vrbadev/Ultrasound_Test_Prototype/STM32CubeIDE/Ultrasound_Test_Prototype/Core/Src/main.c

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
/* Includes ------------------------------------------------------------------*/
#include "main.h"

/* USER CODE BEGIN Includes */
#include <stdio.h>
#include <stdbool.h>
#include <stdlib.h>
/* USER CODE END Includes */

/* USER CODE BEGIN PD */
#ifdef __GNUC__
#define PUTCHAR_PROTOTYPE int __io_putchar(int ch)
#else
#define PUTCHAR_PROTOTYPE int fputc(int ch, FILE *f)
#endif

#define ADC_BUFFER_LEN 1000
#define USART_RX_BUFFER_LEN 256

#define MAX9939_SHDN (0x01 << 7)
#define MAX9939_MEAS (0x01 << 6)

#define MAX9939_VOS_NEG (0x01 << 5)
#define MAX9939_VOS_0_0MV (0x00 << 1)
#define MAX9939_VOS_1_3MV (0x01 << 1)
#define MAX9939_VOS_2_5MV (0x02 << 1)
#define MAX9939_VOS_3_8MV (0x03 << 1)
#define MAX9939_VOS_4_9MV (0x04 << 1)
#define MAX9939_VOS_6_1MV (0x05 << 1)
#define MAX9939_VOS_7_3MV (0x06 << 1)
#define MAX9939_VOS_8_4MV (0x07 << 1)
#define MAX9939_VOS_10_6MV (0x08 << 1)
#define MAX9939_VOS_11_7MV (0x09 << 1)
#define MAX9939_VOS_12_7MV (0x0A << 1)
#define MAX9939_VOS_13_7MV (0x0B << 1)
#define MAX9939_VOS_14_7MV (0x0C << 1)
#define MAX9939_VOS_15_7MV (0x0D << 1)
#define MAX9939_VOS_16_7MV (0x0E << 1)
#define MAX9939_VOS_17_6MV (0x0F << 1)

#define MAX9939_GAIN_0_25X ((0x09 << 1) | 0x01)
#define MAX9939_GAIN_1X ((0x00 << 1) | 0x01)
#define MAX9939_GAIN_10X ((0x01 << 1) | 0x01)
#define MAX9939_GAIN_20X ((0x02 << 1) | 0x01)
#define MAX9939_GAIN_30X ((0x03 << 1) | 0x01)
#define MAX9939_GAIN_40X ((0x04 << 1) | 0x01)
#define MAX9939_GAIN_60X ((0x05 << 1) | 0x01)
#define MAX9939_GAIN_80X ((0x06 << 1) | 0x01)
#define MAX9939_GAIN_120X ((0x07 << 1) | 0x01)
#define MAX9939_GAIN_157X ((0x08 << 1) | 0x01)

/* USER CODE END PD */

ADC_HandleTypeDef hadc1;
DMA_HandleTypeDef hdma_adc1;

SPI_HandleTypeDef hspi1;

TIM_HandleTypeDef htim3;

UART_HandleTypeDef huart1;
DMA_HandleTypeDef hdma_usart1_rx;
DMA_HandleTypeDef hdma_usart1_tx;

/* USER CODE BEGIN PV */
uint32_t millis = 0;
uint32_t delay_end = 0;

uint8_t usart_rx_buffer[USART_RX_BUFFER_LEN];
uint32_t usart_rx_len = 0;

struct {
	uint8_t delimeter[5];
	uint8_t pga_gain : 8;
	int8_t pga_offset : 8;
	uint8_t adc_channel : 8;
	uint32_t id : 32;
	uint8_t adc_buffer[(3 * ADC_BUFFER_LEN) / 4];
	uint8_t dummy[2];
} usart_tx_packet;

uint32_t adc_num_conversions = 0;
uint16_t adc_buffer[ADC_BUFFER_LEN];
bool adc_dma_half_complete = false;
bool adc_dma_complete = false;

struct {
	uint8_t shdn;
	uint8_t meas;
	int gain;
	int offset;
} max9939_settings;

struct {
	char shdn_ch;
	char meas_ch;
	char* gain_str;
	char offset_sign;
	char* offset_str;
} max9939_info;
/* USER CODE END PV */

void SystemClock_Config(void);
static void MX_GPIO_Init(void);
static void MX_DMA_Init(void);
static void MX_ADC1_Init(void);
static void MX_SPI1_Init(void);
static void MX_USART1_UART_Init(void);
static void MX_TIM3_Init(void);
/* USER CODE BEGIN 0 */
PUTCHAR_PROTOTYPE {
	HAL_UART_Transmit(&huart1, (uint8_t*) &ch, 1, HAL_MAX_DELAY);
	return ch;
}

void delay(uint32_t ms) {
	delay_end = millis + ms;
	while (millis < delay_end);
}

void adc_set_channel(uint32_t ch)
{
	HAL_ADC_Stop_DMA(&hadc1);
	ADC_ChannelConfTypeDef sConfig = {0};
	sConfig.Channel = ch;
	sConfig.Rank = ADC_REGULAR_RANK_1;
	sConfig.SamplingTime = ADC_SAMPLINGTIME_COMMON_1;
	if (HAL_ADC_ConfigChannel(&hadc1, &sConfig) != HAL_OK)
	{
	Error_Handler();
	}
	HAL_ADC_Start_DMA(&hadc1, (uint32_t*) adc_buffer, ADC_BUFFER_LEN);
}

void compress_12bit_data(bool first_half)
{
	uint16_t* start = first_half ? (uint16_t*) adc_buffer : (uint16_t*) &(adc_buffer[ADC_BUFFER_LEN/2]);
	uint32_t o = 0;
	for (uint32_t i = 0; i < ADC_BUFFER_LEN / 2; i+=2) {
		usart_tx_packet.adc_buffer[o] = (uint8_t) (start[i] & 0x00FF);
		o++;
		usart_tx_packet.adc_buffer[o] = (uint8_t) ((start[i] & 0x0F00) >> 8) | ((start[i+1] & 0x0F00) >> 4);
		o++;
		usart_tx_packet.adc_buffer[o] = (uint8_t) (start[i+1] & 0x00FF);
		o++;
	}
	usart_tx_packet.id++;
}

void max9939_write(uint8_t reg)
{
	HAL_GPIO_WritePin(SPI1_NSS_GPIO_Port, SPI1_NSS_Pin, GPIO_PIN_RESET);
	delay(1);
	HAL_SPI_Transmit(&hspi1, &reg, 1, HAL_MAX_DELAY);
	while (hspi1.State == HAL_SPI_STATE_BUSY);
	HAL_GPIO_WritePin(SPI1_NSS_GPIO_Port, SPI1_NSS_Pin, GPIO_PIN_SET);
	delay(1);
}

void max9939_apply_settings()
{
	max9939_write((((uint8_t) max9939_settings.gain) << 1) | 0x01);

	int tmp = max9939_settings.offset;
	if (tmp < 0) {
		tmp = -tmp;
		if (tmp >= 0 && tmp <= 15) {
			max9939_write(max9939_settings.shdn | max9939_settings.meas | ((((uint8_t) tmp) << 1) | MAX9939_VOS_NEG));
		}
	} else {
		if (tmp >= 0 && tmp <= 15) {
			max9939_write(max9939_settings.shdn | max9939_settings.meas | (((uint8_t) tmp) << 1));
		}
	}
}

/* USER CODE END 0 */

/**
  * @brief  The application entry point.
  * @retval int
  */
int main(void)
{
  /* MCU Configuration--------------------------------------------------------*/

  /* Reset of all peripherals, Initializes the Flash interface and the Systick. */
  HAL_Init();

  /* Configure the system clock */
  SystemClock_Config();

  /* Initialize all configured peripherals */
  MX_GPIO_Init();
  MX_DMA_Init();
  MX_ADC1_Init();
  MX_SPI1_Init();
  MX_USART1_UART_Init();
  MX_TIM3_Init();
  /* USER CODE BEGIN 2 */
  //HAL_ADC_Start_IT(&hadc1);
  HAL_TIM_PWM_Start(&htim3, TIM_CHANNEL_1);

  HAL_UART_Receive_DMA(&huart1, usart_rx_buffer, USART_RX_BUFFER_LEN);

  max9939_settings.shdn = 0x00;
  max9939_settings.meas = 0x00;
  max9939_settings.gain = 8;
  max9939_settings.offset = 10;
  max9939_apply_settings();

  for(int i = 0; i < sizeof(usart_tx_packet.delimeter); i++) { usart_tx_packet.delimeter[i] = 0xFF; }
  usart_tx_packet.id = 0;
  usart_tx_packet.adc_channel = 2;
  usart_tx_packet.pga_gain = (uint8_t) max9939_settings.gain;
  usart_tx_packet.pga_offset = (int8_t) max9939_settings.offset;

  HAL_ADC_Start_DMA(&hadc1, (uint32_t*) adc_buffer, ADC_BUFFER_LEN);

  HAL_GPIO_WritePin(LED_GPIO_Port, LED_Pin, GPIO_PIN_SET);
  /* USER CODE END 2 */

  /* Infinite loop */
  /* USER CODE BEGIN WHILE */
  int tmp;

  while (1)
  {
    /* USER CODE END WHILE */

    /* USER CODE BEGIN 3 */
	if (usart_rx_len > 0) {
		//printf("Received message: %lu\n", usart_rx_len);
		//HAL_UART_Transmit_DMA(&huart1, usart_rx_buffer, usart_rx_len); // echo
		switch (usart_rx_buffer[0]) {
		case 'S':
			max9939_settings.shdn = (usart_rx_buffer[1] == '1') ? MAX9939_SHDN : 0x00;
			max9939_apply_settings();
			break;
		case 'M':
			max9939_settings.meas = (usart_rx_buffer[1] == '1')? MAX9939_MEAS : 0x00;
			max9939_apply_settings();
			break;
		case 'G':
			usart_rx_buffer[usart_rx_len] = 0;
			tmp = atoi((char*) &(usart_rx_buffer[1]));
			if (tmp >= 0 && tmp <= 9) {
				max9939_settings.gain = tmp;
				usart_tx_packet.pga_gain = (uint8_t) max9939_settings.gain;
				max9939_apply_settings();
			}
			break;
		case 'O':
			usart_rx_buffer[usart_rx_len] = 0;
			tmp = atoi((char*) &(usart_rx_buffer[1]));
			if (tmp >= -15 && tmp <= 15) {
				max9939_settings.offset = tmp;
				usart_tx_packet.pga_offset = (int8_t) max9939_settings.offset;
				max9939_apply_settings();
			}
			break;
		case 'C':
			usart_rx_buffer[usart_rx_len] = 0;
			tmp = atoi((char*) &(usart_rx_buffer[1]));
			switch (tmp) {
			case 0:
				usart_tx_packet.adc_channel = 0;
				adc_set_channel(ADC_CHANNEL_0);
				break;
			case 1:
				usart_tx_packet.adc_channel = 1;
				adc_set_channel(ADC_CHANNEL_1);
				break;
			case 2:
				usart_tx_packet.adc_channel = 2;
				adc_set_channel(ADC_CHANNEL_2);
				break;
			}
			break;
		}
		usart_rx_len = 0;
	}

	if (adc_dma_half_complete) {
			compress_12bit_data(true);
			HAL_UART_Transmit_DMA(&huart1, (uint8_t*) &usart_tx_packet, sizeof(usart_tx_packet));
			//HAL_UART_Transmit_DMA(&huart1, (uint8_t*) adc_buffer, ADC_BUFFER_LEN);

		adc_dma_half_complete = false;
	}

	if (adc_dma_complete) {
			compress_12bit_data(false);
			HAL_UART_Transmit_DMA(&huart1, (uint8_t*) &usart_tx_packet, sizeof(usart_tx_packet));
			//HAL_UART_Transmit_DMA(&huart1, (uint8_t*) (&adc_buffer[ADC_BUFFER_LEN/2]), ADC_BUFFER_LEN);

		adc_dma_complete = false;
	}


	adc_num_conversions = 0;
  }
  /* USER CODE END 3 */
}

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
/* USER CODE BEGIN 4 */
void HAL_ADC_ConvCpltCallback(ADC_HandleTypeDef* hadc)
{
	adc_num_conversions++;
	adc_dma_complete = true;
}


void HAL_ADC_ConvHalfCpltCallback(ADC_HandleTypeDef* hadc)
{
	adc_dma_half_complete = true;
}
/*
void HAL_UART_RxCpltCallback(UART_HandleTypeDef *huart)
{
	//HAL_UART_Receive_DMA(&huart1, usart_rx_buffer, 1);
	HAL_GPIO_TogglePin(LED_GPIO_Port, LED_Pin);
	usart_rx_buffer_size++;
}*/


void USART1_RxDMA_Reset(void)
{
	HAL_UART_DMAStop(&huart1);
	hdma_usart1_rx.Instance->CNDTR = 0;
	HAL_UART_Receive_DMA(&huart1, usart_rx_buffer, USART_RX_BUFFER_LEN);
}

void USART1_IDLECallback(void)
{
	HAL_GPIO_TogglePin(LED_GPIO_Port, LED_Pin);
	usart_rx_len = sizeof(usart_rx_buffer) - __HAL_DMA_GET_COUNTER(&hdma_usart1_rx);
	USART1_RxDMA_Reset();
}


/* USER CODE END 4 */
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
