vrbadev/Ultrasound_Test_Prototype/STM32CubeIDE/Ultrasound_Test_Prototype/Core/Inc/main.h

#define LED_Pin GPIO_PIN_14
#define LED_GPIO_Port GPIOC
#define SPI1_NSS_Pin GPIO_PIN_4
#define SPI1_NSS_GPIO_Port GPIOA
